leonardoward/ftdi-development-boards/Images/IMG_20210827_120828.jpg

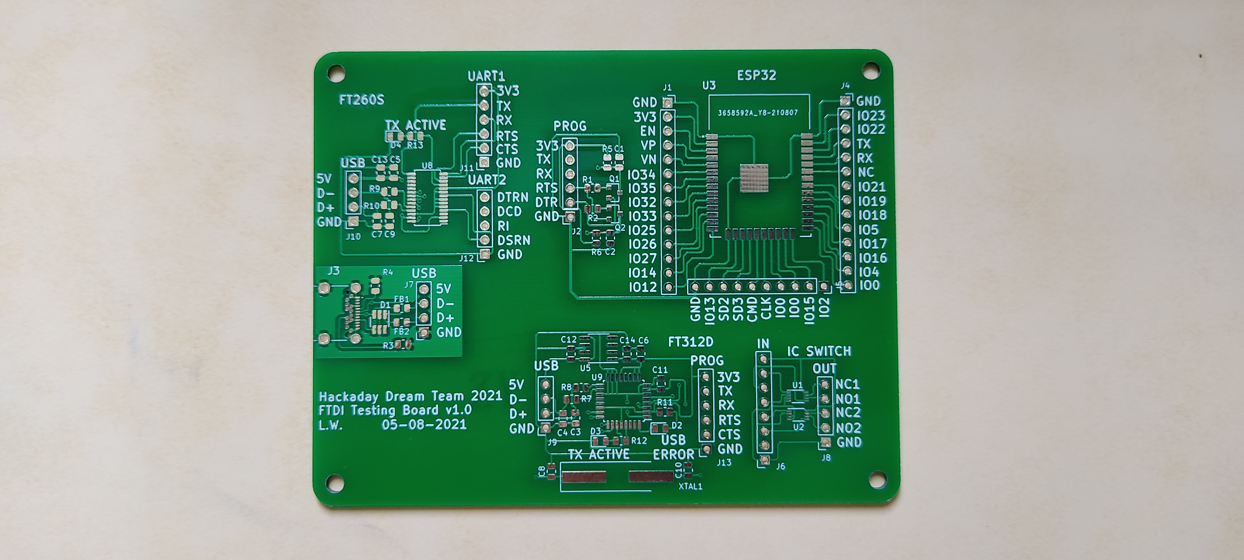
Images/IMG_20210827_120828.jpg
