leonardoward/ftdi-development-boards/Images/IMG_20210827_120922.jpg

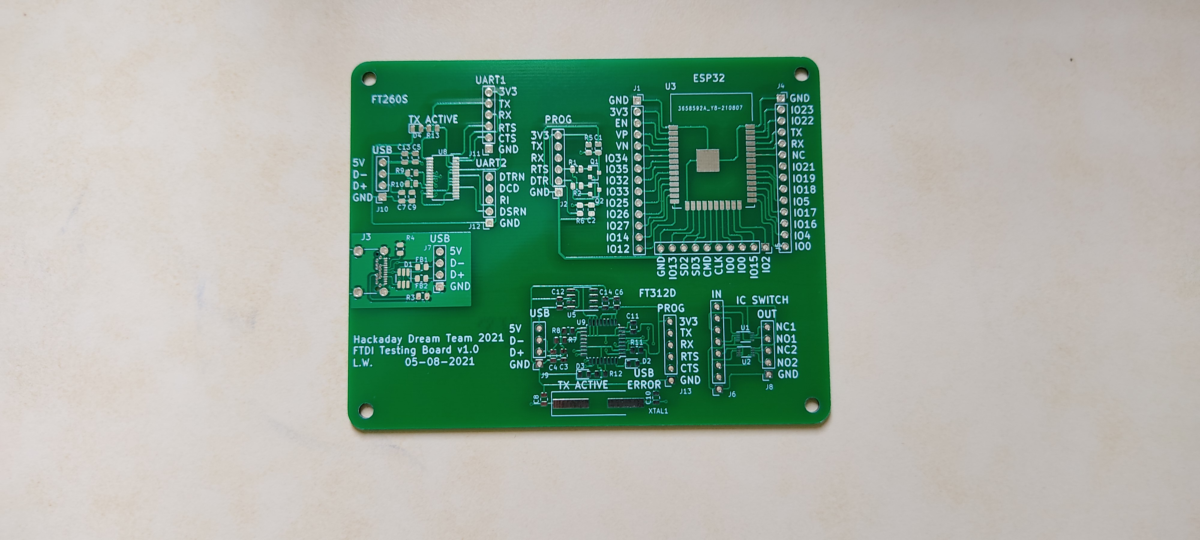
Images/IMG_20210827_120922.jpg
